canvasus/Beatmaster2k/sequencer.cpp

#include "sequencer.h"

Track track0(0, "T0", LP_BLUE);
Track track1(1, "T1", LP_CYAN);
Track track2(2, "T2", LP_PURPLE);
Track track3(3, "T3", LP_PINK);
Track track4(4, "T4", LP_ORANGE);
Track track5(5, "T5", LP_GREEN);
Track track6(6, "T6", LP_YELLOW);
const uint8_t nrTracks = 7;
Track *tracks[nrTracks] = {&track0, &track1, &track2, &track3, &track4, &track5, &track6};

sequencerData SequencerData;

uint8_t sequencerState      = STATE_STOPPED;
uint8_t columnTimer         = 0;
uint16_t  oneTickUs         = 1000 * 60000 / (SequencerData.bpm * ticksPerBeat);
uint8_t sequencerEditMode   = MODE_PATTERNEDIT;
uint8_t selectionId         = SELECTION_PATTERN;
uint8_t actionId            = ACTION_COPY;
int8_t toolTranspose        = 0;
bool sendClock              = false;
uint8_t playMode            = PLAYMODE_NONE;

uint8_t currentTrack        = 0;
uint8_t currentPattern      = 0;
int16_t currentEvent        = -1;
uint8_t currentScene        = 0;
uint8_t currentArrPosition  = 0;
uint8_t currentArrPositionLength = 0;
uint8_t fourthCounter = 0;

uint8_t sceneLengthColumns = 16; // TEMPORARY, MOVE TO SequencerData if used

TrackEvent eventClipBoard[NR_TRACK_EVENTS];
uint8_t nrClipBoardEvents = 0;
Pattern patternClipBoard;

IntervalTimer sequencerUpdateTimer;

MIDIcallback outputNoteOnFunctions[] = {voiceNoteOn, serialMidiNoteOn, deviceNoteOn, midi1NoteOn, midi2NoteOn, midi3NoteOn, midi4NoteOn, midi5NoteOn};
MIDIcallback outputNoteOffFunctions[] = {voiceNoteOff, serialMidiNoteOff, deviceNoteOff, midi1NoteOff, midi2NoteOff, midi3NoteOff, midi4NoteOff, midi5NoteOff};
String outputNames[] = {"Dummy", "Serial", "USB device", "USB 0", "USB 1", "USB 2", "USB 3", "USB 4"};
uint8_t nrOutputFunctions = sizeof(outputNoteOnFunctions)/sizeof(outputNoteOnFunctions[0]);
const String noYesSelected[] = {"No", "Yes", "Selected"};

elapsedMicros debugTimer;

// ---- SEQUENCER CONTROL ----

void initSequencer()
{
  sequencerUpdateTimer.priority(100); 
  for (uint8_t sceneId = 0;sceneId < NR_SCENES; sceneId++) SequencerData.sceneColors[sceneId] = LP_GREEN;
  for (uint8_t arrId = 0;arrId < NR_ARRPOSITIONS; arrId++) SequencerData.arrangement[arrId] = NO_SCENE;
  sequencerUpdateTimer.begin(tickTracks, oneTickUs); 
}

void tickTracks()
{
  // 24 ppq
  if (sequencerState == STATE_RUNNING)
  {
    for (uint8_t trackId = 0;trackId < NR_TRACKS; trackId++) tracks[trackId]->tickTrack();
    if (sendClock) sendMidiClock();
    fourthCounter++;
    if (fourthCounter > ( ticksPerBeat - 1 )) fourthCounter = 0;
  }
  else fourthCounter = 0;
}

void startSequencer()
{
   LP1.setPadColor(CCstartStop, LP_GREEN);
   if (playMode == PLAYMODE_CHAIN_FROM_START)
   {
    currentArrPosition = 0;
    currentScene = SequencerData.arrangement[currentArrPosition];
    setSceneNr(SequencerData.arrangement[currentArrPosition]);
   }
   LP1.setPadColor(CCindicator, LP_CYAN);
   if (sendClock) sendMidiStart();
   sequencerState = STATE_RUNNING;
}

void stopSequencer()
{
  if (sendClock) sendMidiStop();
  LP1.setPadColor(CCstartStop, LP_RED);
  LP1.setPadColor(CCindicator, LP_OFF);
  sequencerState = STATE_STOPPED;
  resetTracks();
  flushTracksPlayedBuffers();
}

void setBpm(float newBpm)
{
  SequencerData.bpm = (uint16_t)newBpm;
  oneTickUs = 1000 * 60000 / (SequencerData.bpm * ticksPerBeat);
  sequencerUpdateTimer.update(oneTickUs); 
}

float getBpm() { return SequencerData.bpm; }

float getPlaymode() { return (float)playMode; }
void setPlaymode(float mode) { playMode = (uint8_t)mode; }

void setMidiClockOnOff(float onOff) { sendClock = (bool)onOff; }
float getMidiClockOnOff() { return sendClock; }


// ---- TRACK CONFIGURATON ----

void setTrackOutput(float value)
{
  uint8_t outputIndex = (uint8_t)value;
  tracks[currentTrack]->setHandleNoteOn(outputNoteOnFunctions[outputIndex]);
  tracks[currentTrack]->setHandleNoteOff(outputNoteOffFunctions[outputIndex]);
  tracks[currentTrack]->outputId = outputIndex;
}

void setCurrentTrack(uint8_t track)
{
  currentTrack = track;
  LP1.page = 0; //min(LP1.page, maxPages);
}

float getTrackOutput() { return tracks[currentTrack]->outputId; }
String getOutputEnum(uint8_t value)
{
  if (value > 2 && value < nrOutputFunctions)
  {
    char buf[16];
    getUsbDeviceName(value - 3, buf, 16);
    outputNames[value] = buf;
  }
  return outputNames[value];
}

float getTrackChannel() { return (float)(tracks[currentTrack]->getTrackChannel()); }
void setTrackChannel(float channel) { tracks[currentTrack]->setTrackChannel((uint8_t)channel); }
String get0_16_note(uint8_t channel)
{
  if (channel < 17) return String(channel);
  else return "NoteVal";
}

float getTrackLengthColumns() { return (float)(tracks[currentTrack]->getPatternLengthColumns(TICKS_PER_COLUMN)); }
void setTrackLengthColumns(float columns) { tracks[currentTrack]->setPatternLengthColumns((uint16_t)columns, TICKS_PER_COLUMN); }

float getTrackDefLength() { return (float)(tracks[currentTrack]->getTrackDefaultNoteLengthTicks()); }
void setTrackDefLength(float length) { tracks[currentTrack]->setTrackDefaultNoteLengthTicks((uint16_t)length); }

float getTrackPatternNr() { return (float)(tracks[currentTrack]->getActivePatternId()); }

void setTrackPatternNr(float patternNr)
{
  if (sequencerState == STATE_STOPPED) tracks[currentTrack]-> setPatternId((uint8_t)patternNr);
  if (sequencerState == STATE_RUNNING) tracks[currentTrack]-> cuePatternId((uint8_t)patternNr);
  currentPattern = (uint8_t)patternNr;
}

float getTransposeStatus() { return (float)tracks[currentTrack]->trackRespondToTranspose; }
void setTransposeStatus(float status) { tracks[currentTrack]->trackRespondToTranspose = (uint8_t)status; }
String getNoYesSelectedEnum(uint8_t value) { return noYesSelected[constrain(value, 0, 2)]; }

void setTranspose(int transpose)
{
  for (uint8_t trackId = 0;trackId < NR_TRACKS; trackId++)
  {
    if (tracks[trackId]->trackRespondToTranspose == 1) tracks[trackId]->transpose = transpose;
    if (tracks[trackId]->trackRespondToTranspose == 2 && trackId == currentTrack ) tracks[trackId]->transpose = transpose;
  }
}


// ---- PATTERN CONFIGURATON ----

void setPatternSpeed(float speed)
{
  uint8_t patternId = tracks[currentTrack]->getActivePatternId();
  tracks[currentTrack]->setPatternSpeed(patternId, (uint8_t)speed);
}

float getPatternSpeed()
{
  uint8_t patternId = tracks[currentTrack]->getActivePatternId();
  return (float)tracks[currentTrack]->getPatternSpeed(patternId);
}

String getPatternSpeedEnum(uint8_t value)
{
  switch (value)
  {
    case PATTERN_SPEED_x1_4: return "x1/4";
    case PATTERN_SPEED_x1_3: return "x1/3";
    case PATTERN_SPEED_x1_2: return "x1/2";
    case PATTERN_SPEED_x1: return "x1";
    case PATTERN_SPEED_x2: return "x2";
    default: return "ERR";
  }
}

void resetTracks()
{
  for (uint8_t trackId = 0;trackId < NR_TRACKS; trackId++) tracks[trackId]->loopResetTrack();
}

void flushTracksPlayedBuffers()
{
  for (uint8_t trackId = 0;trackId < NR_TRACKS; trackId++) tracks[trackId]->flushPlayedBuffer();
}

float getEventLength()
{
  TrackEvent tempEvent = tracks[currentTrack]->getEvent(currentPattern, currentEvent);
  return (float)(tempEvent.noteLength);
}

void setEventLength(float length)
{
  if (currentEvent != -1)
  {
    TrackEvent tempEvent = tracks[currentTrack]->getEvent(currentPattern, currentEvent);
    tempEvent.noteLength = (uint16_t)length;
    tracks[currentTrack]->setEvent(currentPattern, currentEvent, tempEvent);
  }
}


// --- SCENE CONFIGURATION ---

void updateSceneConfiguration(uint8_t sceneId)
{
  // update pattern configuration in selected scene
  for (uint8_t trackId = 0; trackId < NR_TRACKS; trackId++)
  {
    SequencerData.scenes[trackId][sceneId] =  tracks[trackId]->getActivePatternId();
  }
}

void setScene(uint8_t sceneId)
{
  // set or cue patterns from scene
  uint8_t sceneLength = 0;
  for (uint8_t trackId = 0; trackId < NR_TRACKS; trackId++)
  {
    if ( (sequencerState == STATE_STOPPED) && ( tracks[trackId]->getActivePatternId() != SequencerData.scenes[trackId][sceneId]) ) tracks[trackId]->setPatternId(SequencerData.scenes[trackId][sceneId]);
    if (sequencerState == STATE_RUNNING && ( tracks[trackId]->getActivePatternId() != SequencerData.scenes[trackId][sceneId]) ) tracks[trackId]->cuePatternId(SequencerData.scenes[trackId][sceneId]);
    //uint8_t patternLength = tracks[trackId]->getPatternLengthColumns_indexed(SequencerData.scenes[trackId][sceneId], TICKS_PER_COLUMN);
    //sceneLength =  max(sceneLength, patternLength);
  }
  //currentArrPositionLength = sceneLength;
  //Serial.printf("Current scene length: %d\n", sceneLength);
}

float getSceneNr() { return (float)currentScene; }

void setSceneNr(float sceneId)
{
  currentScene = (uint8_t)sceneId;
  setScene(sceneId);
  if (LPdisplayMode == LPMODE_SONG) LPsetPageFromSongData(true);
}

float getSceneColor() { return SequencerData.sceneColors[currentScene]; }
void setSceneColor(float color)
{
  SequencerData.sceneColors[currentScene] = (uint8_t)color;
  LPsetSceneButtonsSceneMode(true);
}


// --- CLIPBOARD TOOLS ---

void setToolSelection(float selection) { selectionId = (uint8_t)selection; }
float getToolSelection() { return (float)selectionId; }
String getSelectionEnum(uint8_t selection)
{
  switch (selection)
  {
    case SELECTION_PATTERN:
      return "Pattern";
      break;
    case SELECTION_COLUMNS:
      return "Columns";
      break;
    case SELECTION_VIEW:
      return "View";
      break;
    case SELECTION_SONG:
      return "Song";
      break;
    default:
      return "ERR";
  }
}

void setToolAction(float action) {actionId = (uint8_t)action;}
float getToolAction() { return (float)actionId;}
String getActionEnum(uint8_t action)
{
  switch (action)
  {
    case ACTION_CLEAR:
      return "Clear";
      break;
    case ACTION_COPY:
      return "Copy";
      break;
    case ACTION_PASTE:
      return "Paste";
      break;
    default:
      return "ERR";
  }
}

void setToolTranspose(float transpose) {toolTranspose = (int8_t)transpose;}
float getToolTranspose() { return (float)toolTranspose;}

void doToolAction()
{
  switch(actionId)
  {
    case ACTION_CLEAR:
      clearSelection();
      break;
    case ACTION_COPY:
      copySelection();
      break;
    case ACTION_PASTE:
      pasteSelection();
      break;
  }
}

void clearEventClipBoard()
{
  for (uint8_t eventId = 0; eventId < NR_TRACK_EVENTS; eventId++) eventClipBoard[eventId] = empty_trackEvent;
  nrClipBoardEvents = 0;
}

void normalizeEventClipBoard()
{
  for(uint8_t clipBoardEventId = 0; clipBoardEventId < nrClipBoardEvents; clipBoardEventId++)
  {
    eventClipBoard[clipBoardEventId].tick = eventClipBoard[clipBoardEventId].tick % (8 * TICKS_PER_COLUMN);
  }
}

void copySelection()
{
  clearEventClipBoard();
  
  if (selectionId == SELECTION_PATTERN) patternClipBoard = tracks[currentTrack]->getPattern(currentPattern);
  
  if (selectionId == SELECTION_COLUMNS || selectionId == SELECTION_VIEW)
  {
    uint8_t noteStart = tracks[currentTrack]->lowerRow;
    uint8_t noteEnd = noteStart + 8;
    uint8_t eventCounter = 0;
    
    if (selectionId == SELECTION_COLUMNS)
    {
      noteStart = 0;
      noteEnd = 127;
    } 
    
    for (uint8_t column = 0; column < 8; column++)
    {
      uint16_t tick = LP1.page * 8 * TICKS_PER_COLUMN + column * TICKS_PER_COLUMN;
      for(uint8_t note = noteStart; note <= noteEnd; note++)
      {
        int16_t eventId = tracks[currentTrack]->getEventId(tick, note);
        if (eventId > -1)
        {
          eventClipBoard[eventCounter] = tracks[currentTrack]->getEvent(currentPattern, eventId);
          eventCounter++;
        }
      }
    }
    nrClipBoardEvents = eventCounter;
    normalizeEventClipBoard();
   }  
}
  

void pasteSelection()
{
  if (selectionId == SELECTION_PATTERN) tracks[currentTrack]->setPattern(currentPattern, patternClipBoard);

  if (selectionId == SELECTION_COLUMNS || selectionId == SELECTION_VIEW)
  {
    uint16_t destinationPageTickStart = LP1.page * 8 * TICKS_PER_COLUMN;
    for(uint8_t clipBoardEventId = 0; clipBoardEventId < nrClipBoardEvents; clipBoardEventId++)
    {
      tracks[currentTrack]->addEvent(eventClipBoard[clipBoardEventId].tick + destinationPageTickStart, 
                                      eventClipBoard[clipBoardEventId].noteValue + toolTranspose, 
                                      eventClipBoard[clipBoardEventId].noteVelocity, 
                                      eventClipBoard[clipBoardEventId].noteLength, 
                                      false);
    }
  }
  
  LPsetPageFromTrackData();
  LPcopy_update(false);
}

void clearSelection()
{
  if (selectionId == SELECTION_PATTERN) tracks[currentTrack]->clearPattern(tracks[currentTrack]->getActivePatternId());
  
  if (selectionId == SELECTION_SONG)
  {
    for (uint8_t arrId = 0;arrId < NR_ARRPOSITIONS; arrId++) SequencerData.arrangement[arrId] = NO_SCENE;
  }
  
  if (selectionId == SELECTION_COLUMNS || selectionId == SELECTION_VIEW)
  {
    uint16_t tickStart = (LP1.page * 8) * TICKS_PER_COLUMN;
    uint16_t tickEnd = tickStart + 8 * TICKS_PER_COLUMN - 1;
    if (selectionId == SELECTION_COLUMNS)
    {
      for(uint8_t note = 0; note < 128; note++) tracks[currentTrack]->removeEvents(tickStart, tickEnd, note);
    }
    if (selectionId == SELECTION_VIEW)
    {
      uint8_t noteStart = tracks[currentTrack]->lowerRow;
      uint8_t noteEnd = noteStart + 8;
      for(uint8_t note = noteStart; note <= noteEnd; note++) tracks[currentTrack]->removeEvents(tickStart, tickEnd, note);
    }
  }
}

// --- SONG MODE, SCENE CHAINING ---

void updateSequencer()
{
  if ( (sequencerState == STATE_RUNNING) && ( (playMode == PLAYMODE_CHAIN_FROM_SELECTION) || (playMode == PLAYMODE_CHAIN_FROM_START) ) ) updateSongMode();
}

void updateSongMode()
{
  // NOTE: many improvements needed. This concept does not handle repetitions of same scene
  
  bool allTracksInCurrentScene = true;
  uint8_t sceneId = SequencerData.arrangement[currentArrPosition];
  static uint8_t sceneAgeColumns = 0;
  
  for (uint8_t trackId = 0; trackId < NR_TRACKS; trackId++)
  {
    if (tracks[trackId]->getActivePatternId() != SequencerData.scenes[trackId][sceneId]) allTracksInCurrentScene = false;
  }
  
  if ( allTracksInCurrentScene && (SequencerData.arrangement[currentArrPosition + 1] != NO_SCENE))
  {
    setSceneNr(SequencerData.arrangement[currentArrPosition + 1]);
    currentArrPosition++;
  }
}

String getSongModeEnum(uint8_t modeId)
{
  switch (modeId)
  {
    case PLAYMODE_NONE: return F("Off");
    case PLAYMODE_CHAIN_FROM_SELECTION: return F("From Selection");
    case PLAYMODE_CHAIN_FROM_START: return F("From Start");
    default: return F("ERR");
  }
}
